PancakeLegend/HackSynth/KiCAD/Mixer/Mixer.kicad_pcb

## KiCad design KiCAD/Mixer/Mixer.kicad_pcb (2025-06-14)

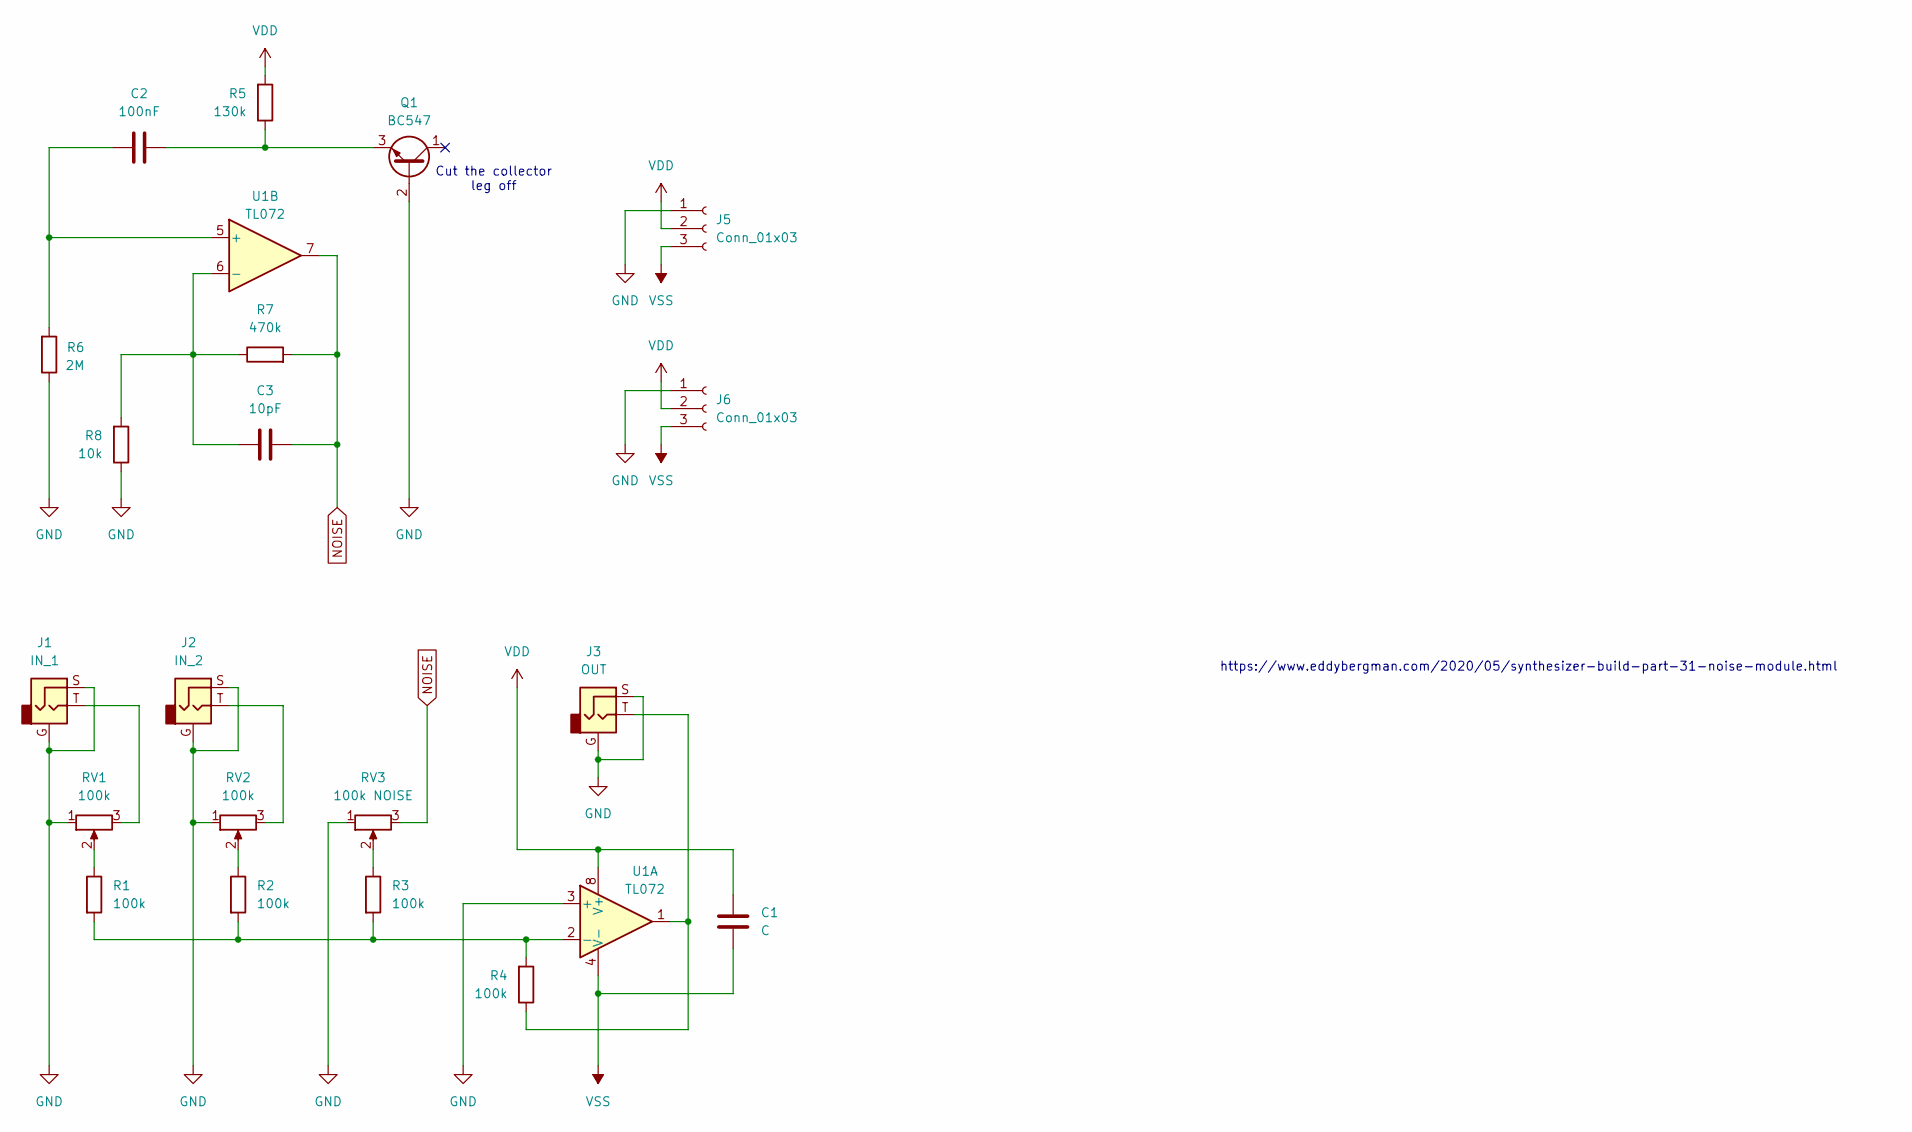
[picture p29: schematic Mixer.kicad_sch, Mixer + Noise Module]

Parts:
C1: C; C_Disc_D5.0mm_W2.5mm_P5.00mm
C2: 100nF; C_Disc_D5.0mm_W2.5mm_P5.00mm
C3: 10pF; C_Disc_D5.0mm_W2.5mm_P5.00mm
J1: IN_1; Jack_3.5mm
J2: IN_2; Jack_3.5mm
J3: OUT; Jack_3.5mm
J5, J6: Conn_01x03; JST_PH_S3B-PH-K_1x03_P2.00mm_Horizontal
Q1: BC547; TO-92_Inline - BC547 - 2-Pin Handsolder
R1, R2, R3, R4: 100k; R_Axial_DIN0207_L6.3mm_D2.5mm_P7.62mm_Horizontal
R5: 130k; R_Axial_DIN0207_L6.3mm_D2.5mm_P7.62mm_Horizontal
R6: 2M; R_Axial_DIN0207_L6.3mm_D2.5mm_P7.62mm_Horizontal
R7: 470k; R_Axial_DIN0207_L6.3mm_D2.5mm_P7.62mm_Horizontal
R8: 10k; R_Axial_DIN0207_L6.3mm_D2.5mm_P7.62mm_Horizontal
RV1, RV2: 100k; Potentiometer_Alps_RK09K_Horizontal
RV3: 100k NOISE; Potentiometer_Alps_RK09K_Horizontal
U1: TL072; DIP-8_W7.62mm_LongPads

Connections:
GND: J1.G, J1.S, J2.G, J2.S, J3.G, J3.S, J5.1, J6.1, Q1.2 (B), R6.1, R8.1, RV1.1, RV2.1, RV3.1, U1.3 (+)
NOISE: C3.2, R7.2, RV3.3, U1.7
unnamed: J1.T, RV1.3
unnamed: J2.T, RV2.3
unnamed: J3.T, R4.1, U1.1
unnamed: C2.2, Q1.3 (E), R5.1
unnamed: R1.1, RV1.2
unnamed: R2.1, RV2.2
unnamed: R3.1, RV3.2
unnamed: R1.2, R2.2, R3.2, R4.2, U1.2 (-)
unnamed: C2.1, R6.2, U1.5 (+)
unnamed: C3.1, R7.1, R8.2, U1.6 (-)
VDD: C1.1, J5.2, J6.2, R5.2, U1.8 (V+)
VSS: C1.2, J5.3, J6.3, U1.4 (V-)

Notes on the sheet:
https://www.eddybergman.com/2020/05/synthesizer-build-part-31-noise-module.html
Cut the collector leg off

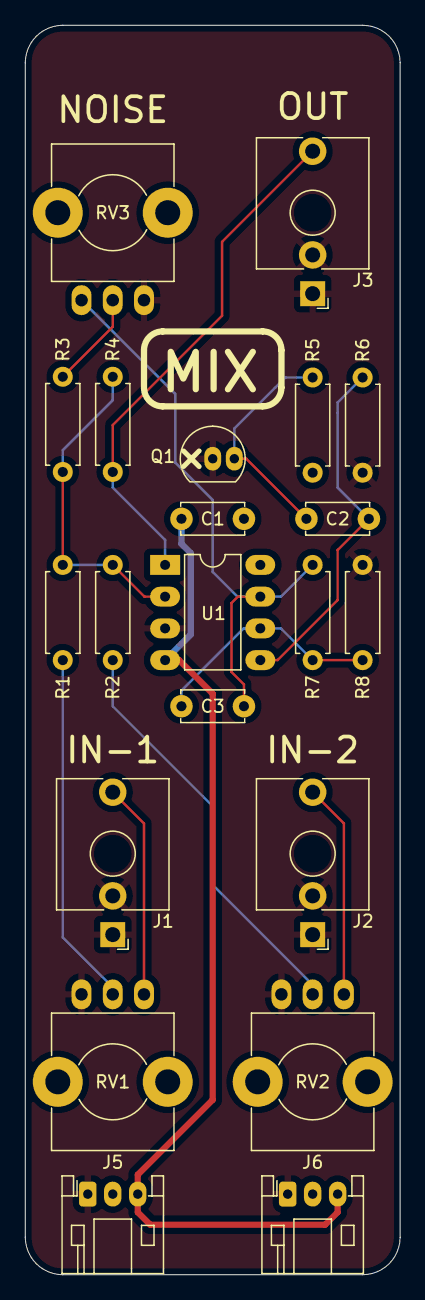
[picture p30: board Mixer.kicad_pcb from above]

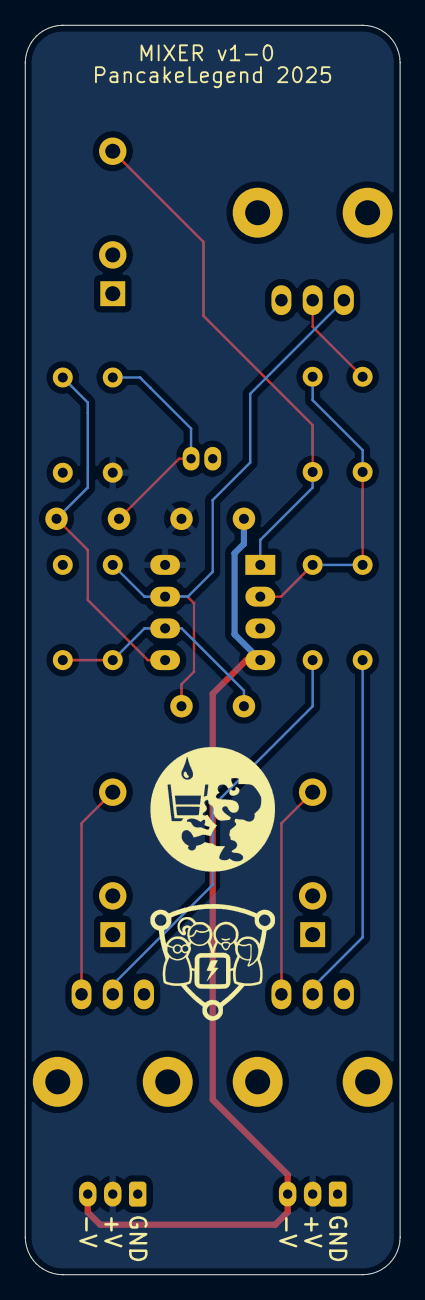
[picture p31: board Mixer.kicad_pcb from below]

Board: 2 copper layers, 30.0 x 100.0 mm, 23 parts (2 on the bottom side), 14 nets.

Other parts of the board:
Ref**: Val**; CCHS Logo - 10mm
Ref**#2: Val**; PancakeLegend Logo - 10mm
